MOSH-Insa-Toulouse/2022-2023-4gp-gomond-guyot/photos/app_bluetooth2.jpg

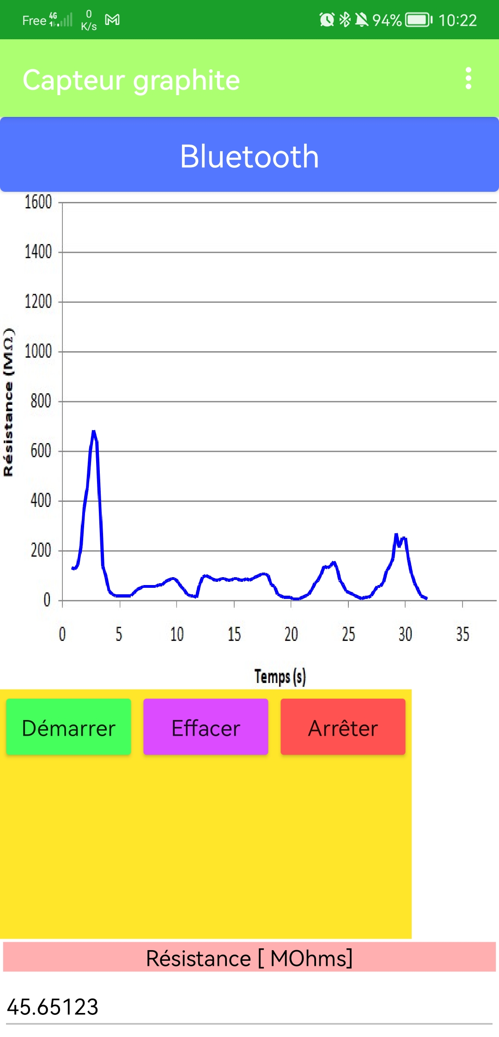
photos/app_bluetooth2.jpg
