MOSH-Insa-Toulouse/2022-2023-4gp-gomond-guyot/photos/callibration_angle0.jpg

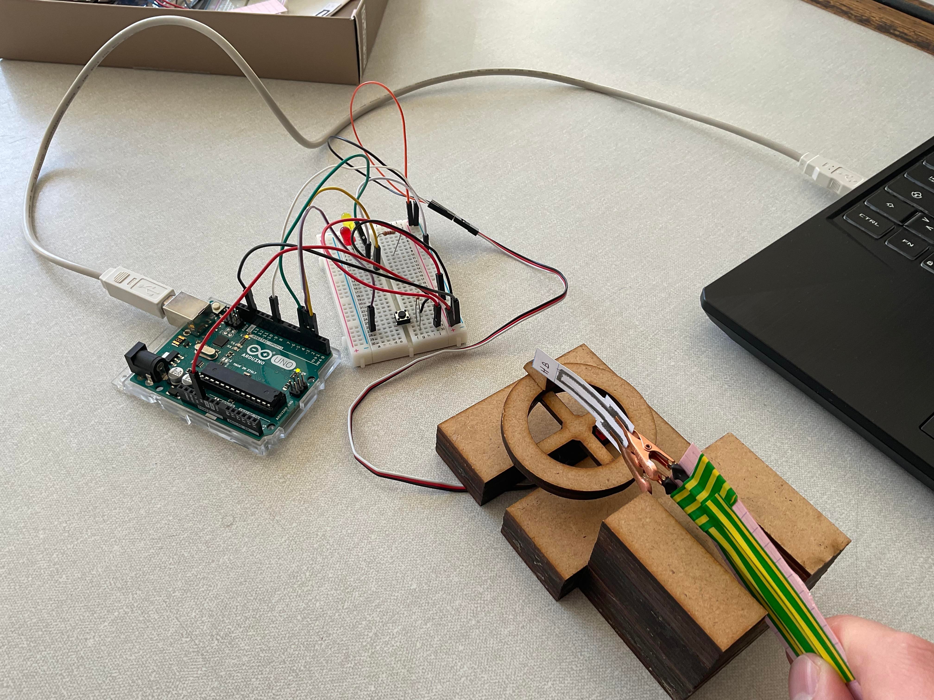
photos/callibration_angle0.jpg
