MOSH-Insa-Toulouse/2022-2023-4gp-gomond-guyot/photos/flex_sensor.jpg

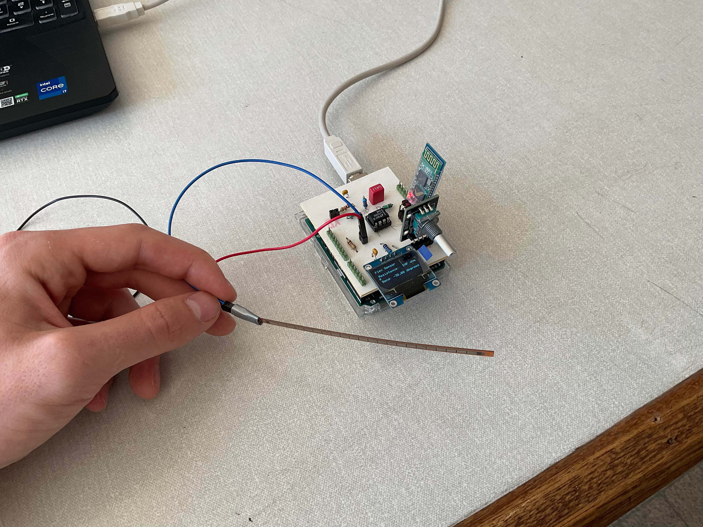
photos/flex_sensor.jpg
