MOSH-Insa-Toulouse/2022-2023-4gp-gomond-guyot/photos/graphite_sensor2.jpg

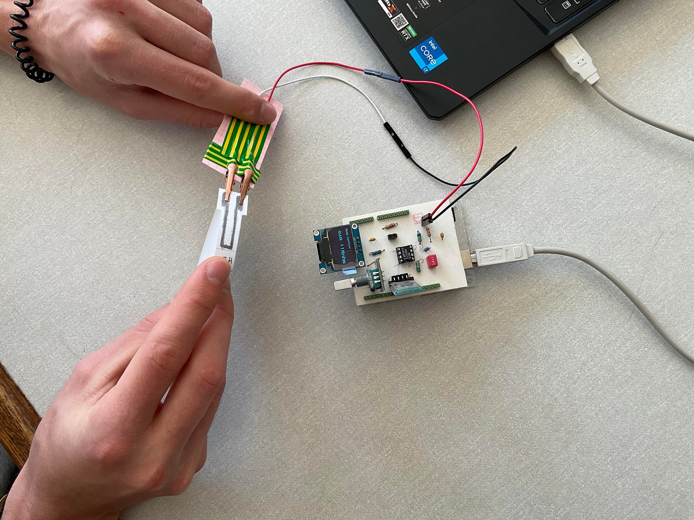
photos/graphite_sensor2.jpg
